caidenpuma/CAPSTONE_PROJECT/PCB Files/draft_2_low_power_chip.kicad_sch

## KiCad design PCB Files/draft_2_low_power_chip.kicad_sch (2025-07-15)

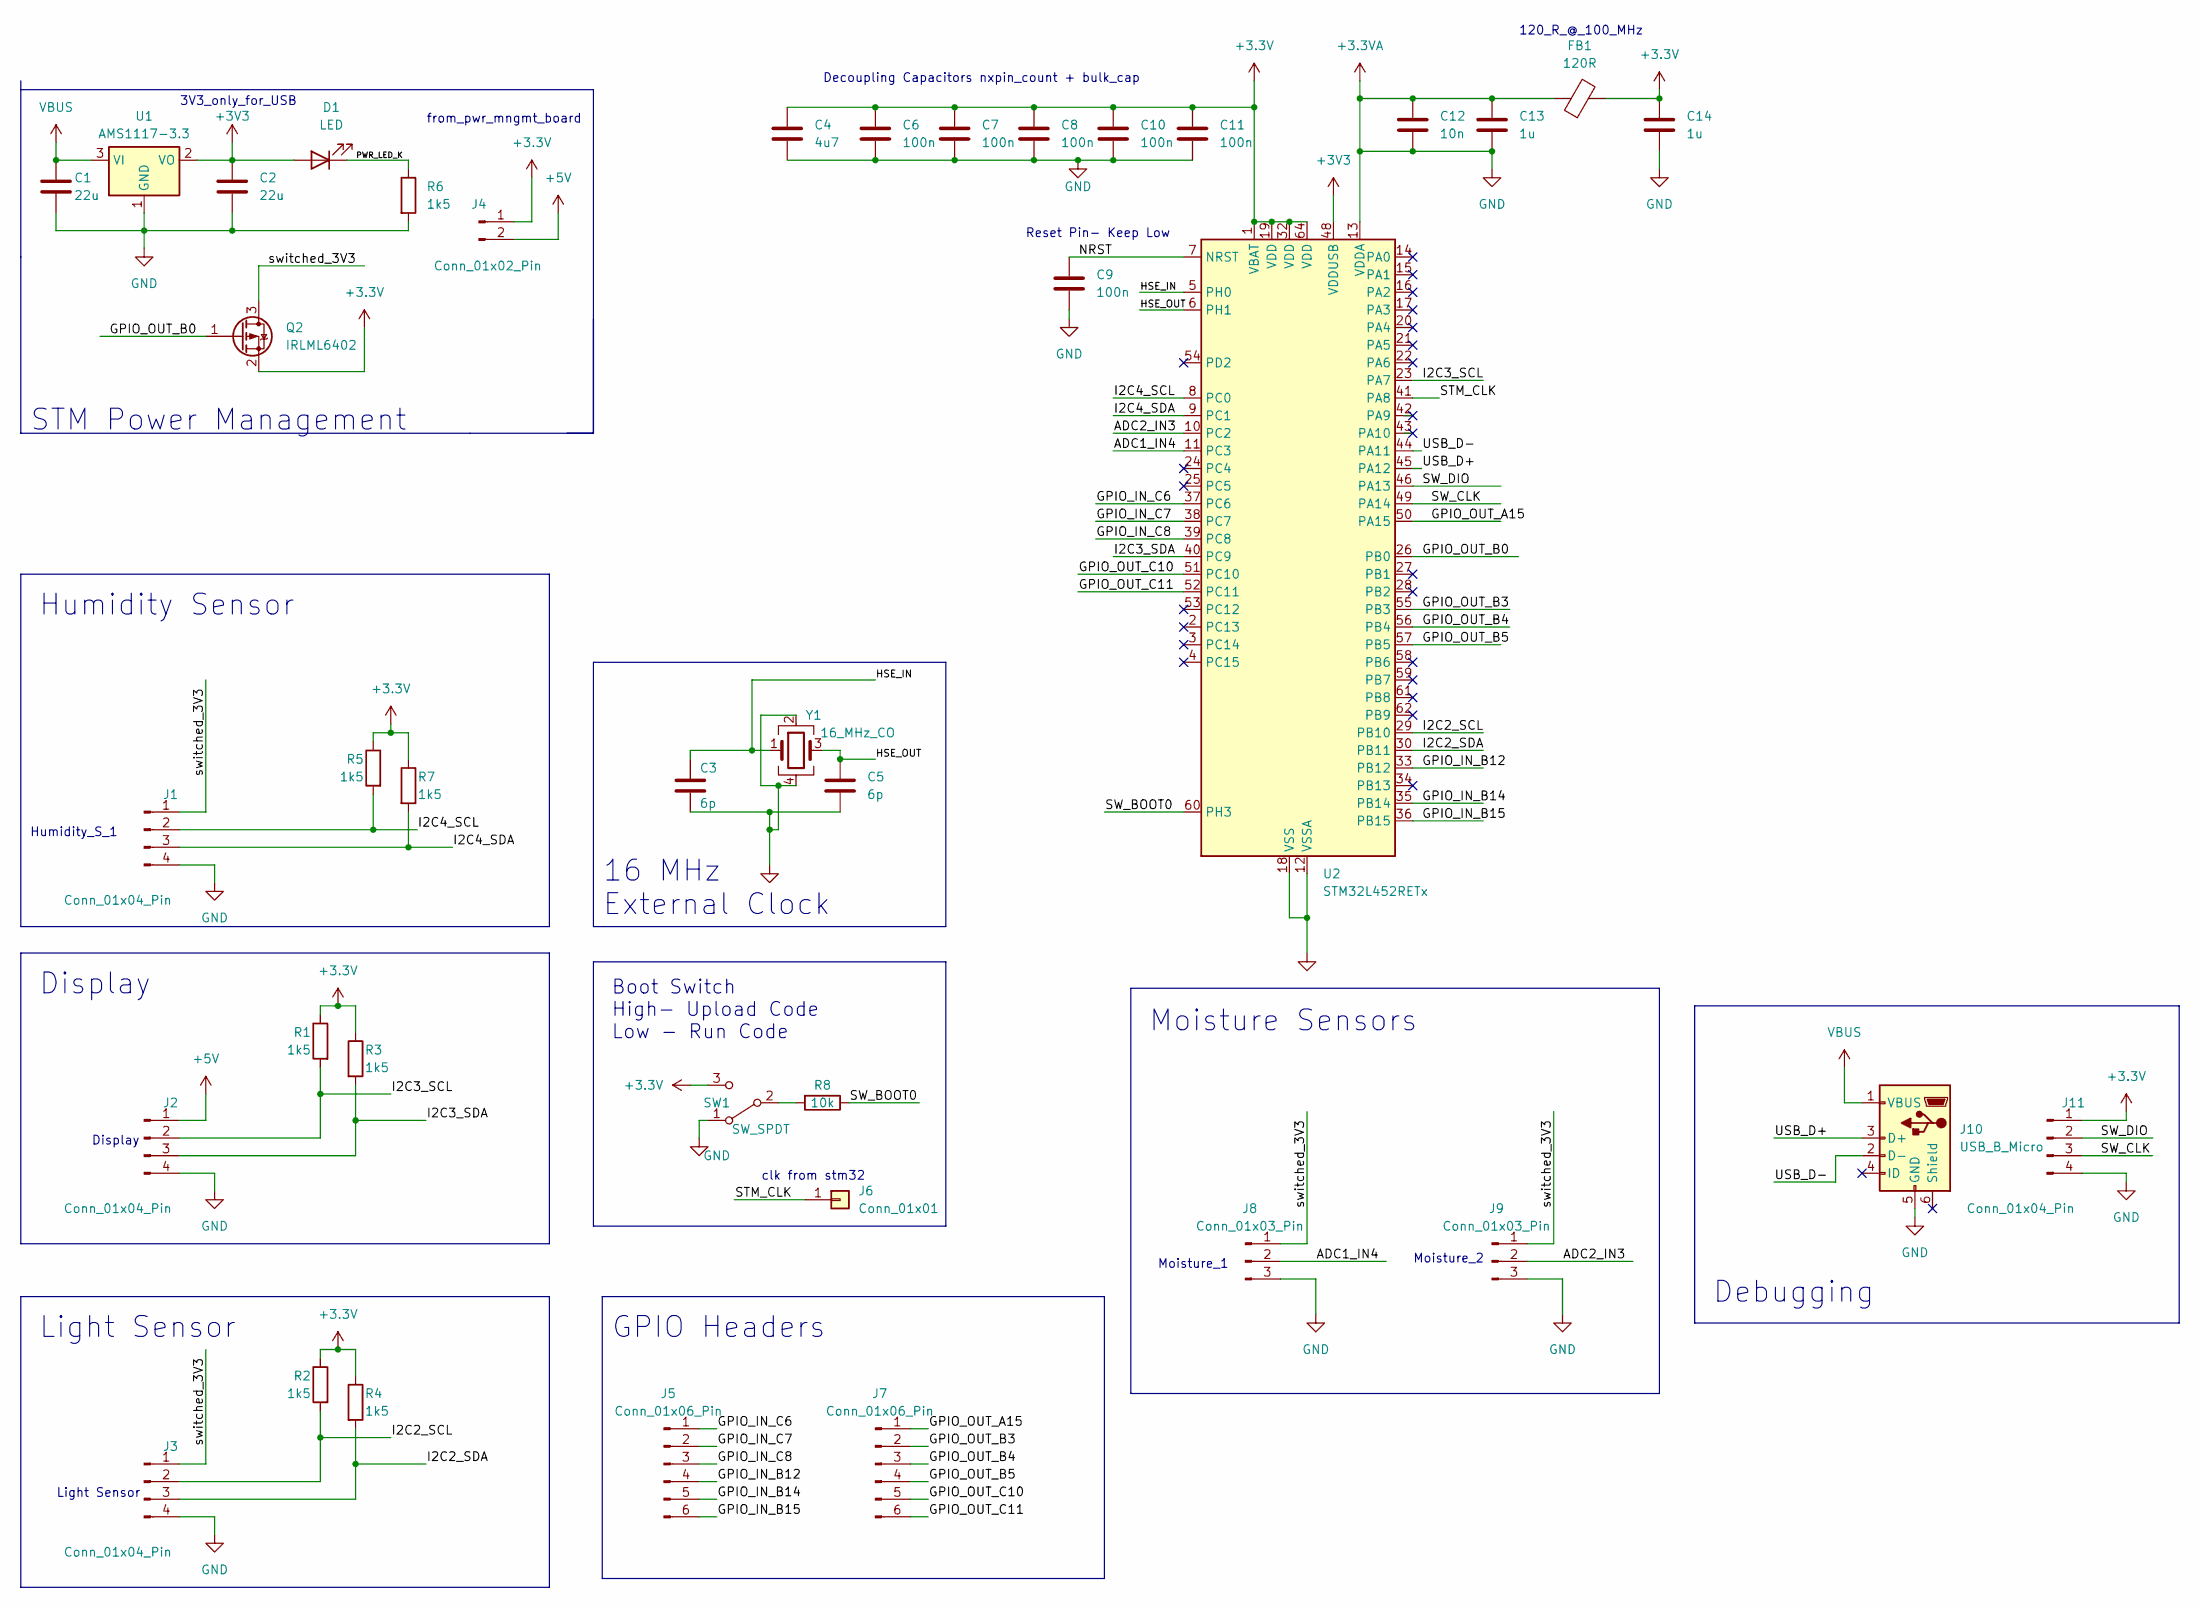
[picture p7: schematic draft_2_low_power_chip.kicad_sch]

Parts:
C1, C2: 22u; C_0805_2012Metric
C3, C5: 6p; C_0402_1005Metric
C4: 4u7; C_0603_1608Metric
C6, C7, C8, C9, C10, C11: 100n; C_0402_1005Metric
C12: 10n; C_0402_1005Metric
C13, C14: 1u; C_0402_1005Metric
D1: LED; LED_0603_1608Metric
FB1: 120R; L_0603_1608Metric
J1, J2, J3, J11: Conn_01x04_Pin; PinHeader_1x04_P2.54mm_Vertical
J4: Conn_01x02_Pin; Molex_KK-396_A-41791-0002_1x02_P3.96mm_Vertical
J5, J7: Conn_01x06_Pin; JST_EH_B6B-EH-A_1x06_P2.50mm_Vertical
J6: Conn_01x01; Hirose_DF63R-1P-3.96DSA_1x01_P3.96mm_Vertical
J8, J9: Conn_01x03_Pin; JST_NV_B03P-NV_1x03_P5.00mm_Vertical
J10: USB_B_Micro; USB_Micro-B_Wuerth_629105150521
Q2: IRLML6402; SOT-23
R1, R2, R3, R4, R5, R6, R7: 1k5; R_0402_1005Metric
R8: 10k; R_0402_1005Metric
SW1: SW_SPDT; SW_Lever_1P2T_NKK_GW12LxH
U1: AMS1117-3.3; SOT-223-3_TabPin2
U2: STM32L452RETx; LQFP-64_10x10mm_P0.5mm
Y1: 16_MHz_CO; Crystal_SMD_3225-4Pin_3.2x2.5mm

Connections:
+3.3V: C4.1, C6.1, C7.1, C8.1, C10.1, C11.1, C14.1, FB1.2, J4.1, J11.1, Q2.2 (S), R1.1, R2.1, R3.1, R4.1, R5.1, R7.1, SW1.3 (C), U2.1 (VBAT), U2.19 (VDD), U2.32 (VDD), U2.64 (VDD)
+3.3VA: C1.2, C2.2, C3.2, C4.2, C5.2, C6.2, C7.2, C8.2, C9.2, C10.2, C11.2, C12.1, C12.2, C13.1, C13.2, C14.2, FB1.1, J1.4, J2.4, J3.4, J8.3, J9.3, J10.5 (GND), J11.4, R6.2, SW1.1 (A), U1.1 (GND), U2.12 (VSSA), U2.13 (VDDA), U2.18 (VSS), U2.31 (VSS), U2.47 (VSS), U2.63 (VSS), Y1.2, Y1.4
+3V3: C2.1, D1.2 (A), U1.2 (VO), U2.48 (VDDUSB)
+5V: J2.1, J4.2
ADC1_IN4: J8.2, U2.11 (PC3)
ADC2_IN3: J9.2, U2.10 (PC2)
GPIO_IN_B12: J5.4, U2.33 (PB12)
GPIO_IN_B14: J5.5, U2.35 (PB14)
GPIO_IN_B15: J5.6, U2.36 (PB15)
GPIO_IN_C6: J5.1, U2.37 (PC6)
GPIO_IN_C7: J5.2, U2.38 (PC7)
GPIO_IN_C8: J5.3, U2.39 (PC8)
GPIO_OUT_A15: J7.1, U2.50 (PA15)
GPIO_OUT_B0: Q2.1 (G), U2.26 (PB0)
GPIO_OUT_B3: J7.2, U2.55 (PB3)
GPIO_OUT_B4: J7.3, U2.56 (PB4)
GPIO_OUT_B5: J7.4, U2.57 (PB5)
GPIO_OUT_C10: J7.5, U2.51 (PC10)
GPIO_OUT_C11: J7.6, U2.52 (PC11)
HSE_IN: C3.1, U2.5 (PH0), Y1.1
HSE_OUT: C5.1, U2.6 (PH1), Y1.3
I2C2_SCL: J3.2, R2.2, U2.29 (PB10)
I2C2_SDA: J3.3, R4.2, U2.30 (PB11)
I2C3_SCL: J2.2, R1.2, U2.23 (PA7)
I2C3_SDA: J2.3, R3.2, U2.40 (PC9)
I2C4_SCL: J1.2, R5.2, U2.8 (PC0)
I2C4_SDA: J1.3, R7.2, U2.9 (PC1)
NRST: C9.1, U2.7 (NRST)
unnamed: R8.2, SW1.2 (B)
PWR_LED_K: D1.1 (K), R6.1
STM_CLK: J6.1, U2.41 (PA8)
SW_BOOT0: R8.1, U2.60 (PH3)
SW_CLK: J11.3, U2.49 (PA14)
SW_DIO: J11.2, U2.46 (PA13)
USB_D+: J10.3 (D+), U2.45 (PA12)
USB_D-: J10.2 (D-), U2.44 (PA11)
VBUS: C1.1, J10.1 (VBUS), U1.3 (VI)
switched_3V3: J1.1, J3.1, J8.1, J9.1, Q2.3 (D)

Notes on the sheet:
Decoupling Capacitors nxpin_count + bulk_cap
16 MHz External Clock
GPIO Headers
Moisture_2
from_pwr_mngmt_board
Light Sensor
3V3_only_for_USB
120_R_@_100_MHz
Reset Pin- Keep Low
clk from stm32
Boot Switch High- Upload Code Low - Run Code
STM Power Management
Display
Humidity Sensor
Humidity_S_1
Debugging
Moisture_1
Moisture Sensors
