caidenpuma/CAPSTONE_PROJECT/STM IDE Project/Core/Inc/light_sensor.h

/* SoilSense
 * Header file for light sensor operation
 * Sensor: VEML7700
 */

#include <stdint.h>

#ifndef INC_LIGHT_SENSOR_H_
#define INC_LIGHT_SENSOR_H_

extern uint32_t light_24h_counter;
extern uint32_t light_3day_counter;

void mins_in_optimal_light(int light_level);
void get_light_value();
void calc_high_intensity();
void check_light_intensity();
void check_light_time();

#endif /* INC_LIGHT_SENSOR_H_ */
