caidenpuma/CAPSTONE_PROJECT/STM IDE Project/Core/Inc/temp_rh_sensor.h

/* SoilSense
 * Header file for temp/humidity sensor operation
 * Sensor: DHT22
 */

#ifndef INC_TEMP_RH_SENSOR_H_
#define INC_TEMP_RH_SENSOR_H_

void get_temp_and_rh_value();
void check_temp();
void check_rh();

#endif /* INC_TEMP_RH_SENSOR_H_ */
